zueblin/Polaron/Doc/Images/bottomview.jpg

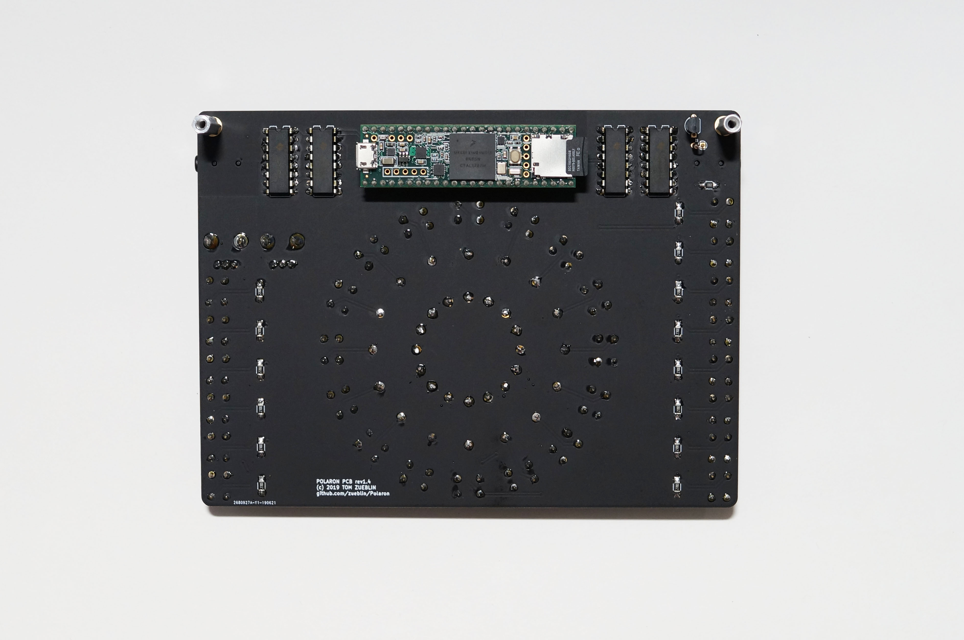
Doc/Images/bottomview.jpg
