zueblin/Polaron/Doc/Images/firmware/arduino-ide-board-selection.png

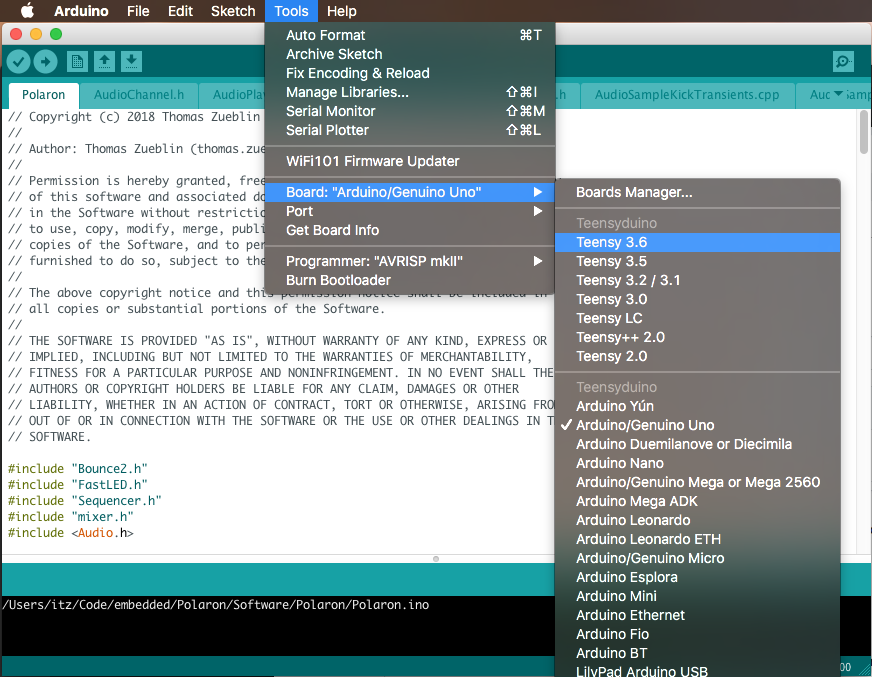
Doc/Images/firmware/arduino-ide-board-selection.png
