zueblin/Polaron/Doc/Images/firmware/arduino-ide-initial.png

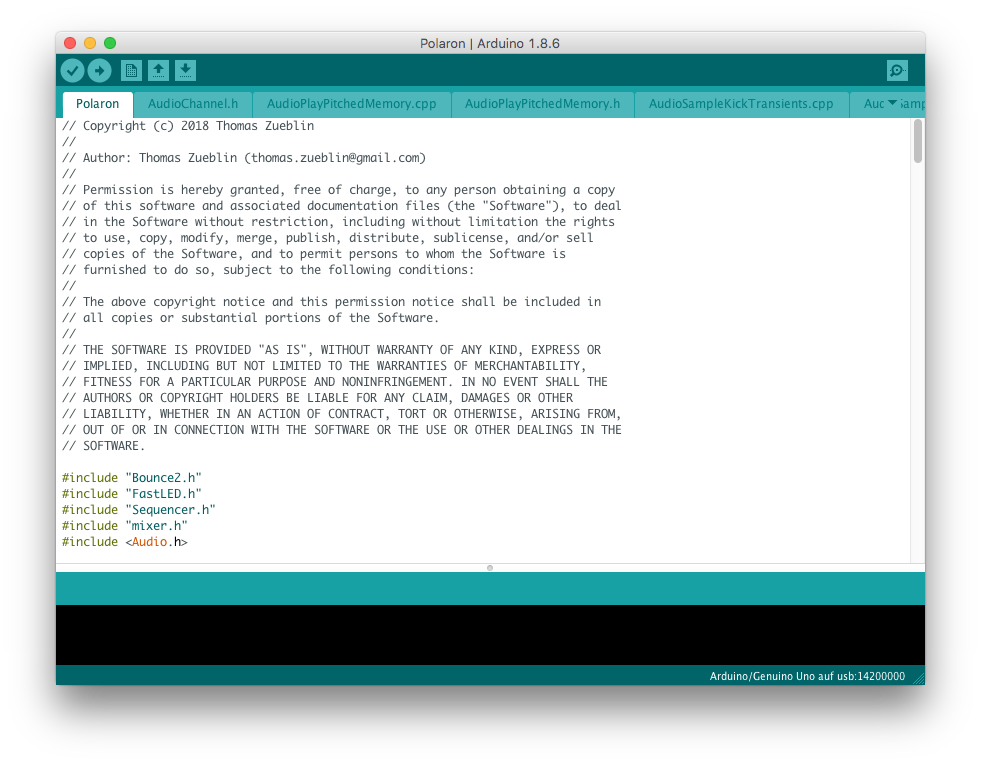
Doc/Images/firmware/arduino-ide-initial.png
