zueblin/Polaron/Doc/Images/firmware/arduino-ide-successful-compilation.png

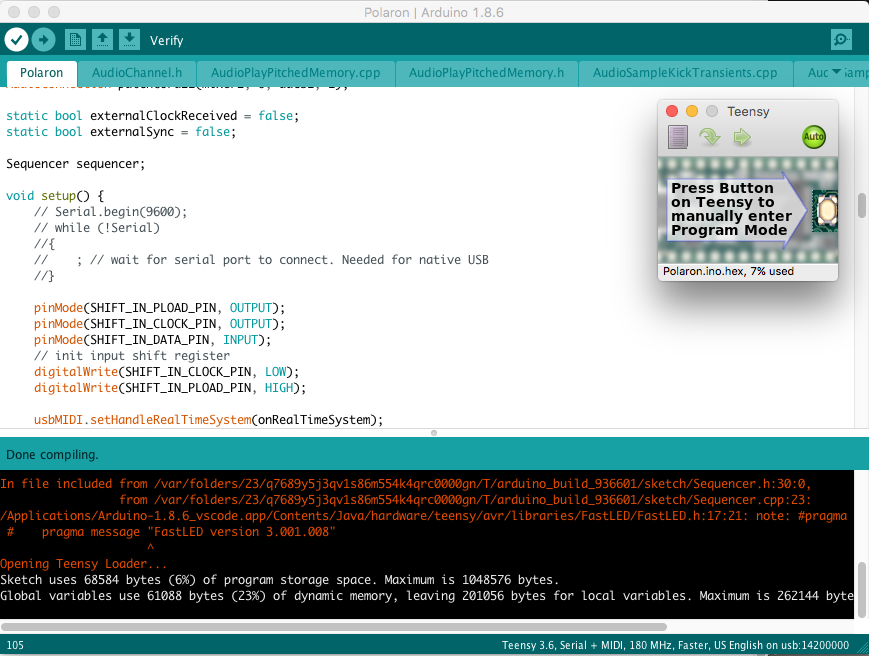
Doc/Images/firmware/arduino-ide-successful-compilation.png
