zueblin/Polaron/Doc/Images/firmware/arduino-ide-upload.png

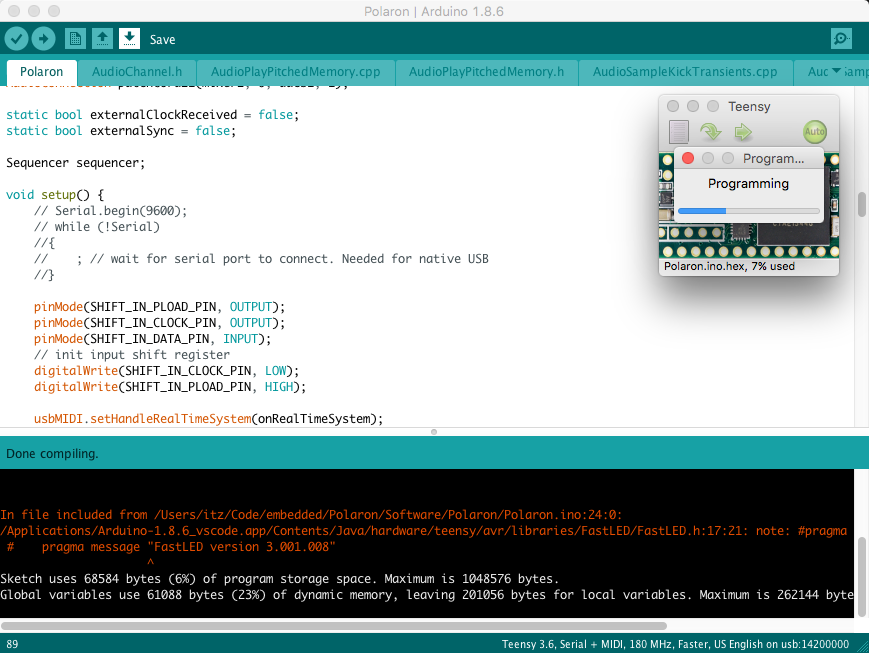
Doc/Images/firmware/arduino-ide-upload.png
