zueblin/Polaron/Doc/Images/firmware/arduino-ide-usbtype-selection.png

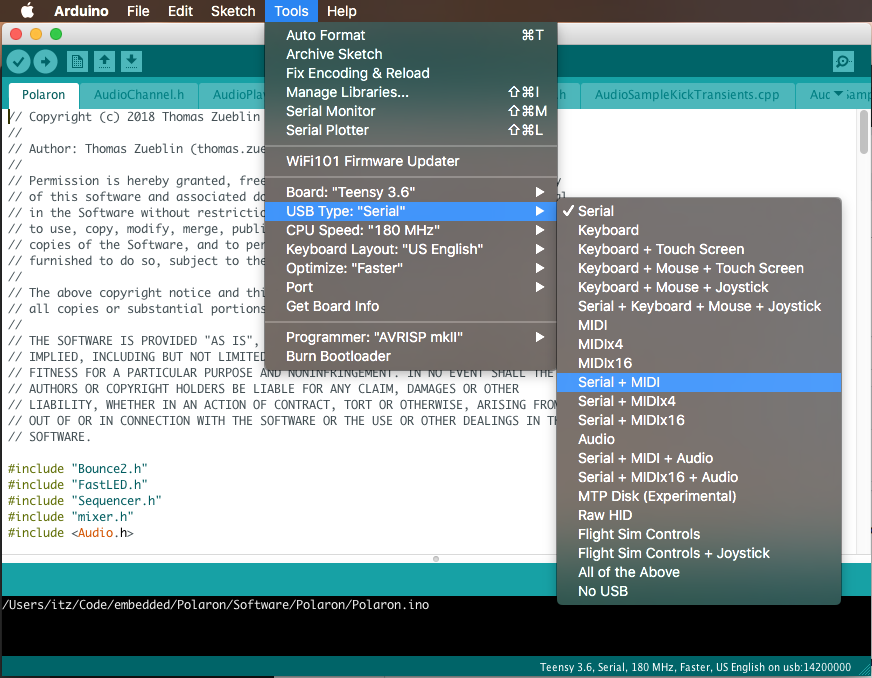
Doc/Images/firmware/arduino-ide-usbtype-selection.png
