zueblin/Polaron/Doc/Images/pcb.png

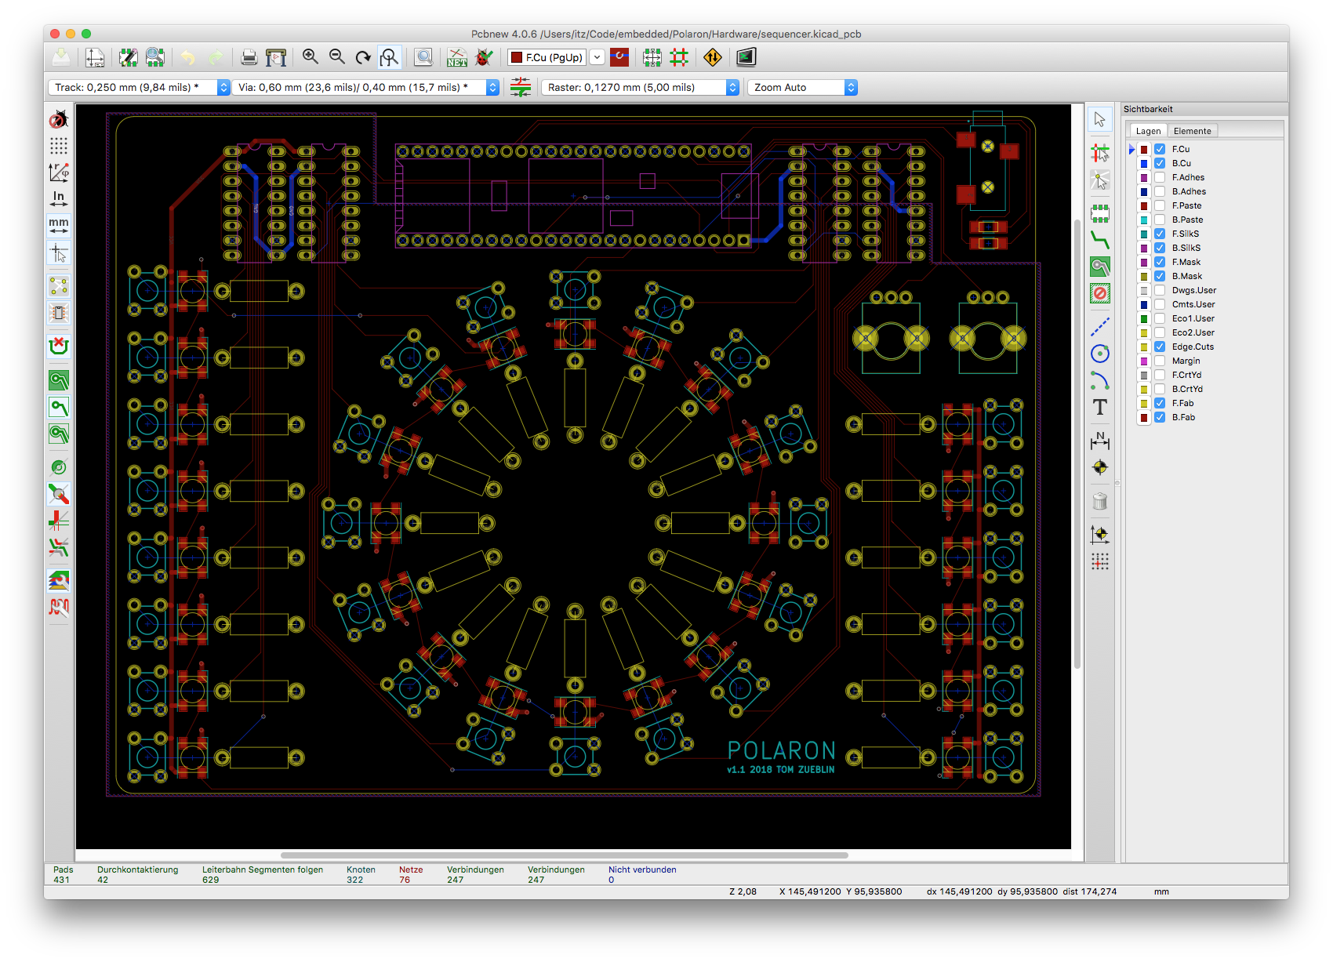
Doc/Images/pcb.png
