zueblin/Polaron/Doc/Images/topview.jpg

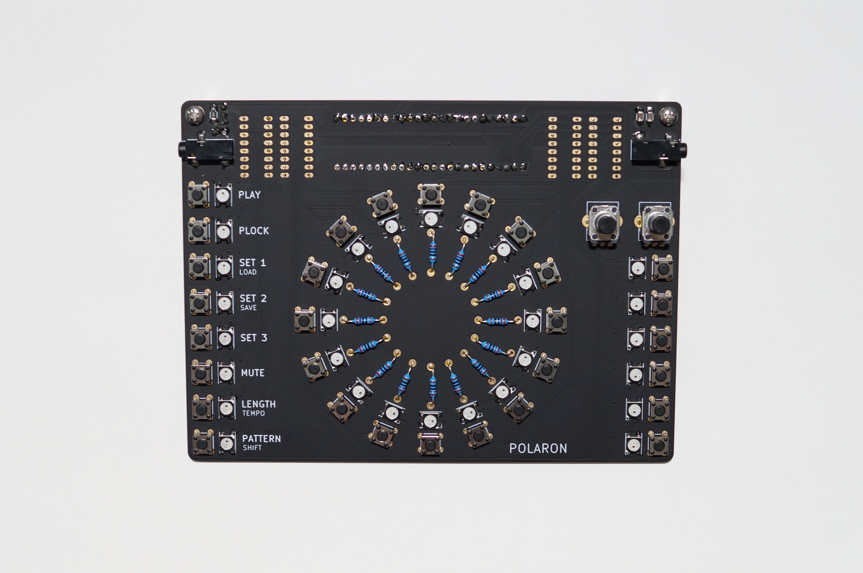
Doc/Images/topview.jpg
