zueblin/Polaron/Doc/Images/assembly/rev-1.4/parts.jpg

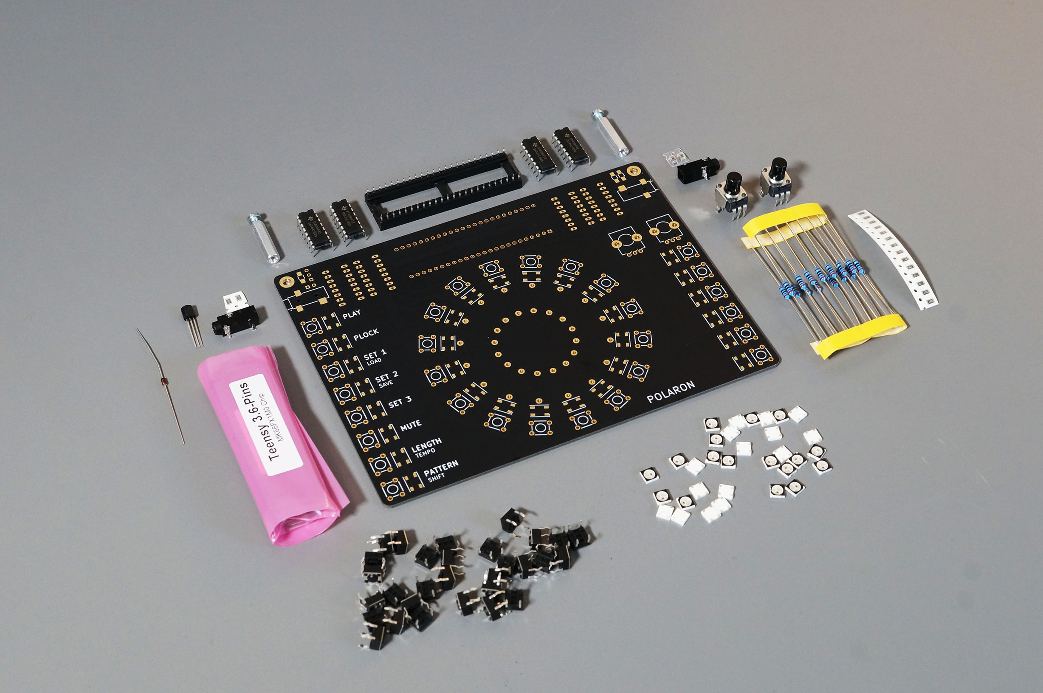
Doc/Images/assembly/rev-1.4/parts.jpg
