zueblin/Polaron/Doc/Images/assembly/done.jpg

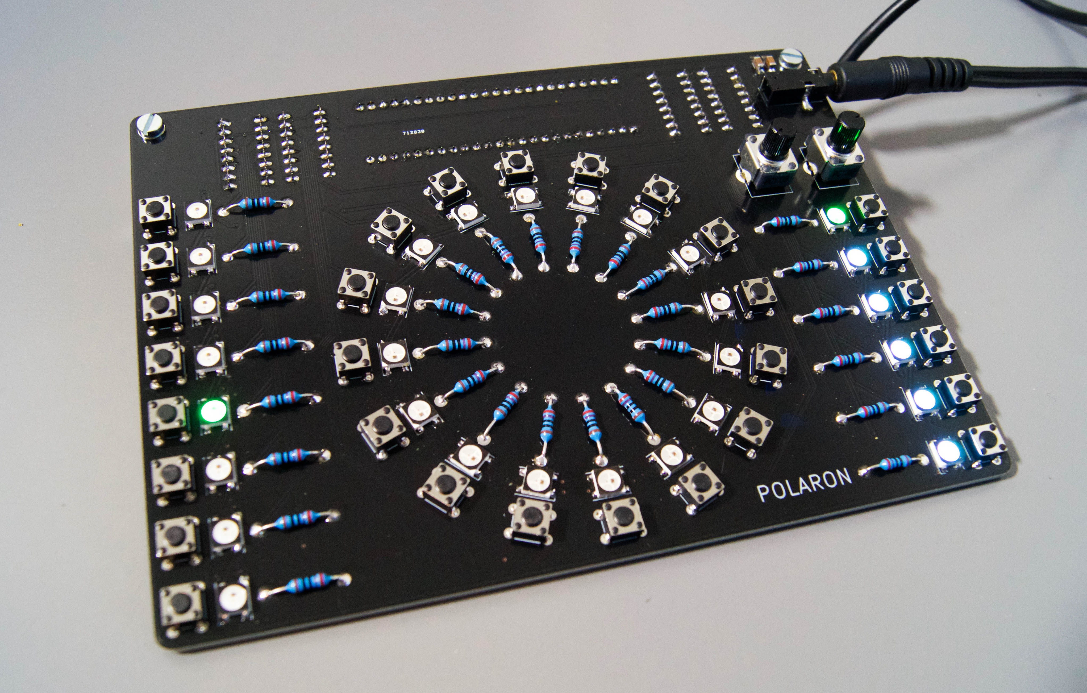
Doc/Images/assembly/done.jpg
