zueblin/Polaron/Doc/Images/assembly/led-dot-1.jpg

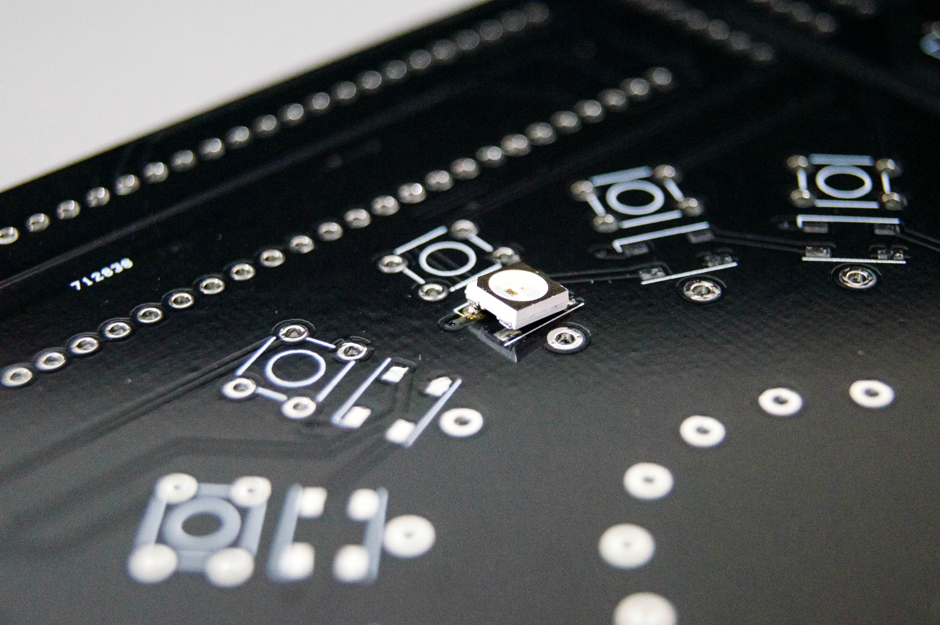
Doc/Images/assembly/led-dot-1.jpg
