zueblin/Polaron/Doc/Images/assembly/led-dot-2.jpg

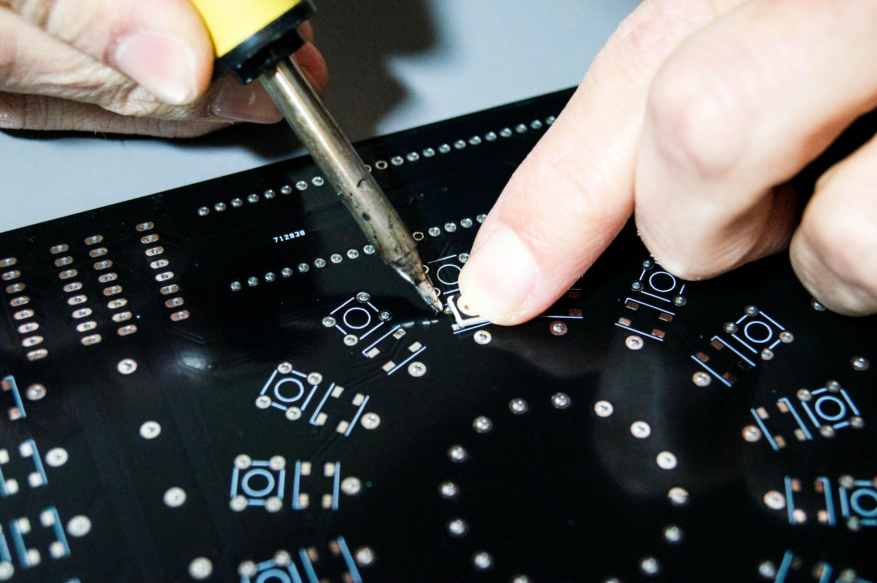
Doc/Images/assembly/led-dot-2.jpg
