zueblin/Polaron/Doc/Images/assembly/led-dot.jpg

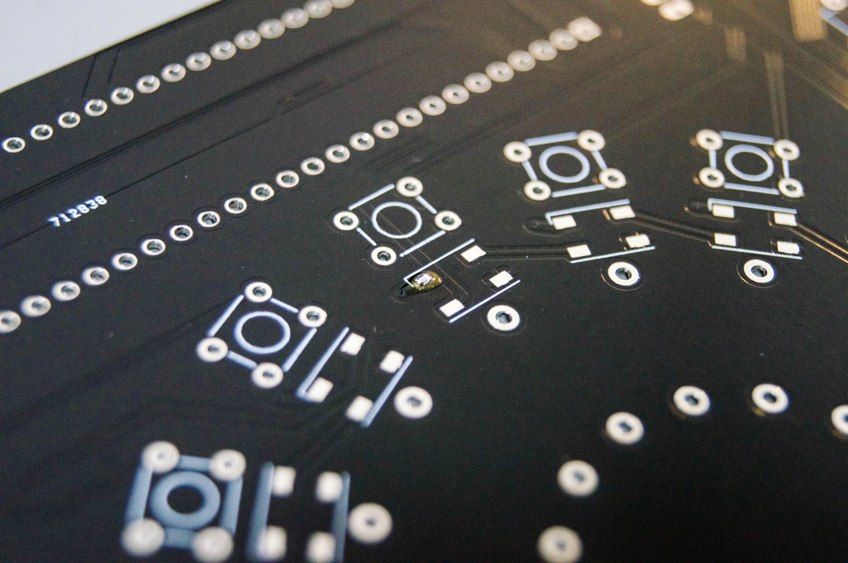
Doc/Images/assembly/led-dot.jpg
