zueblin/Polaron/Doc/Images/assembly/led-placement.jpg

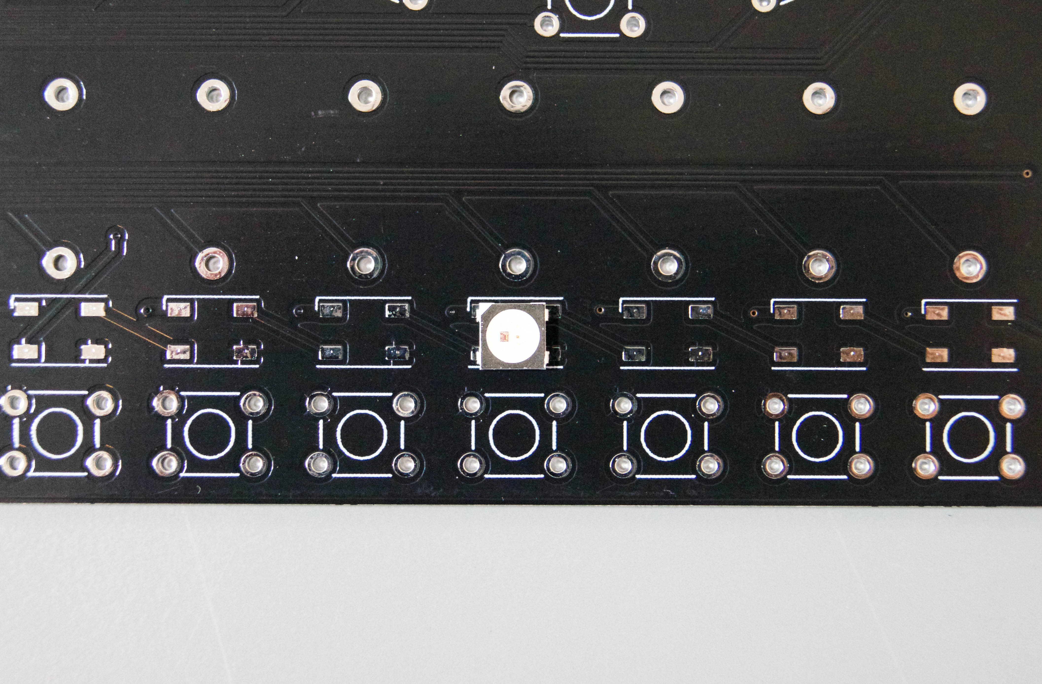
Doc/Images/assembly/led-placement.jpg
