zueblin/Polaron/Doc/Images/assembly/leds-done.jpg

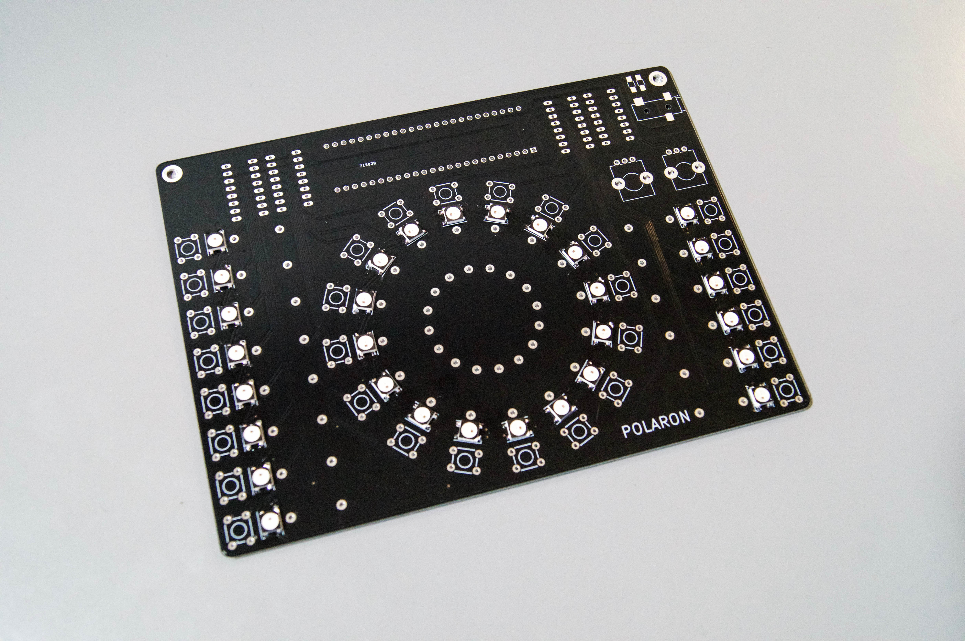
Doc/Images/assembly/leds-done.jpg
