zueblin/Polaron/Doc/Images/assembly/push-buttons.jpg

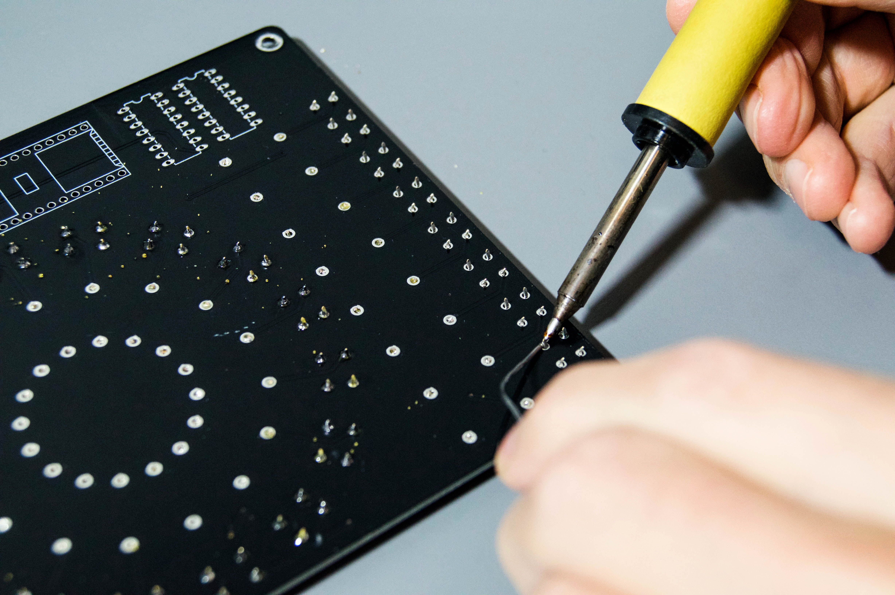
Doc/Images/assembly/push-buttons.jpg
