zueblin/Polaron/Doc/Images/assembly/resistors-1.jpg

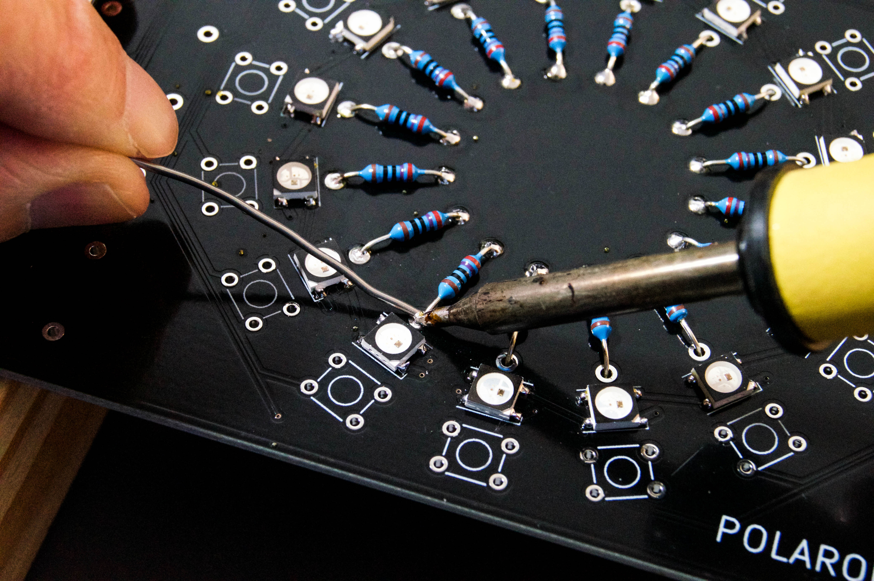
Doc/Images/assembly/resistors-1.jpg
