zueblin/Polaron/Doc/Images/assembly/resistors-cut.jpg

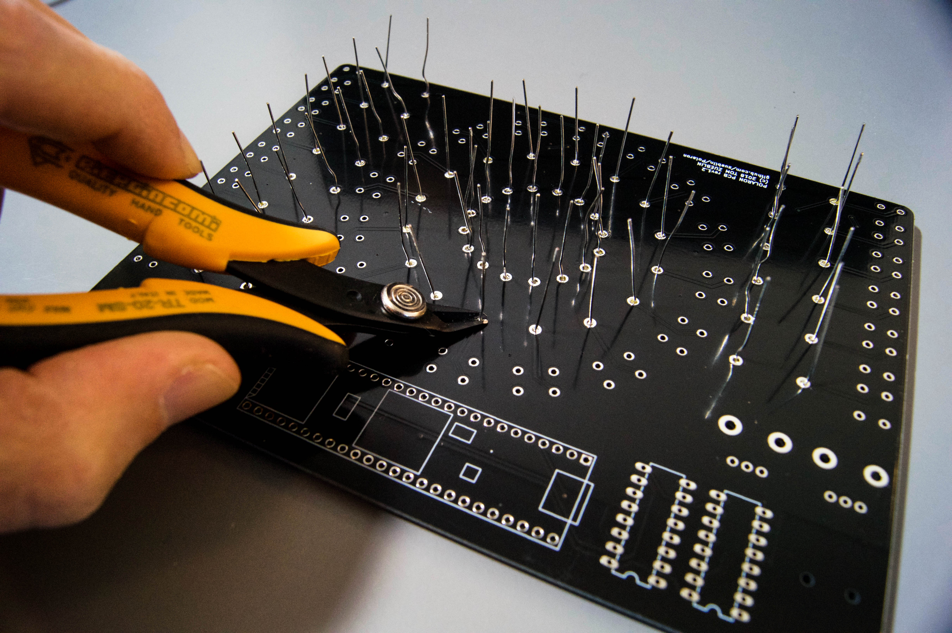
Doc/Images/assembly/resistors-cut.jpg
