zueblin/Polaron/Doc/Images/assembly/rev-1.4/audio-out-capacitors-done.jpg

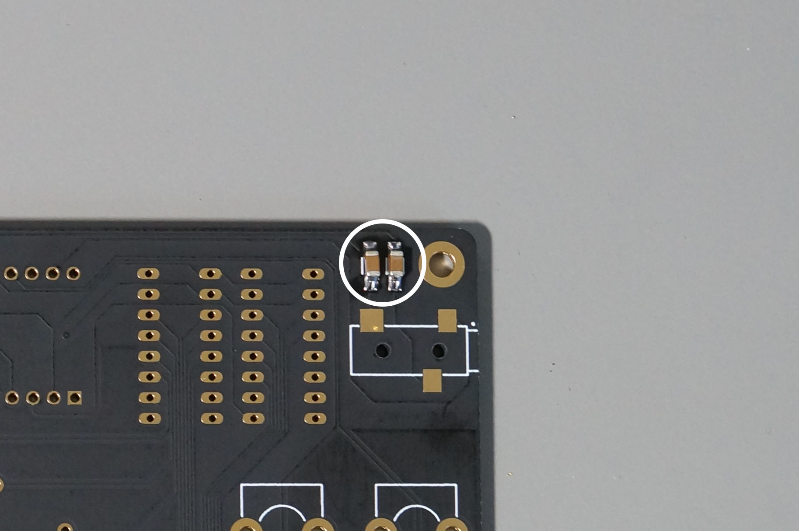
Doc/Images/assembly/rev-1.4/audio-out-capacitors-done.jpg
