zueblin/Polaron/Doc/Images/assembly/rev-1.4/led-dot-2.jpg

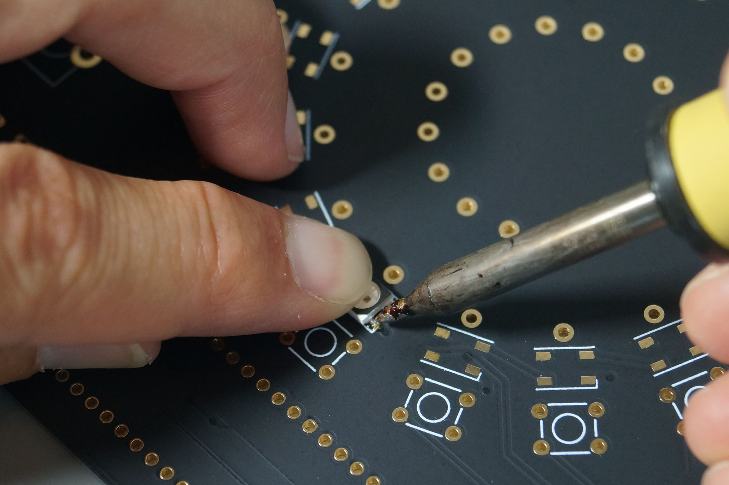
Doc/Images/assembly/rev-1.4/led-dot-2.jpg
