zueblin/Polaron/Doc/Images/assembly/rev-1.4/led-dot.jpg

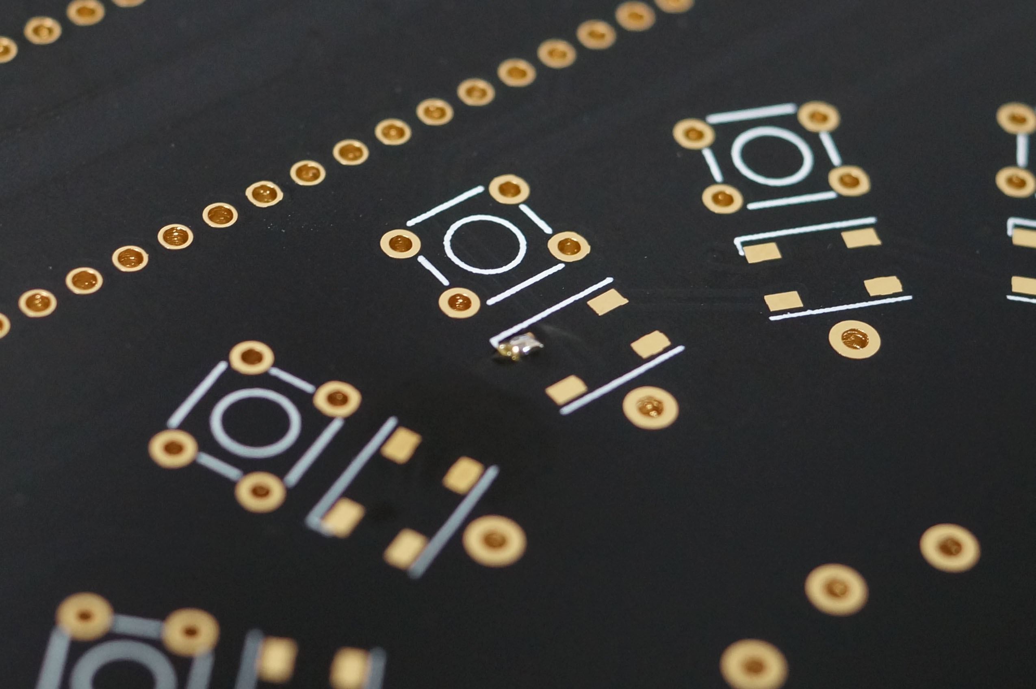
Doc/Images/assembly/rev-1.4/led-dot.jpg
