zueblin/Polaron/Doc/Images/assembly/rev-1.4/led-placement.jpg

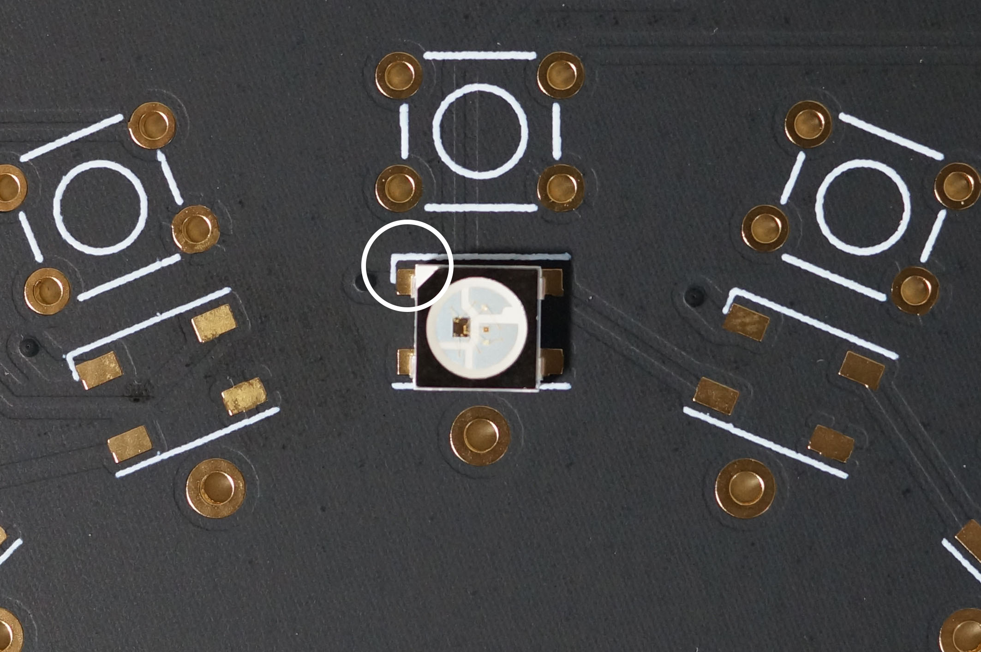
Doc/Images/assembly/rev-1.4/led-placement.jpg
