zueblin/Polaron/Doc/Images/assembly/rev-1.4/plugs-done.jpg

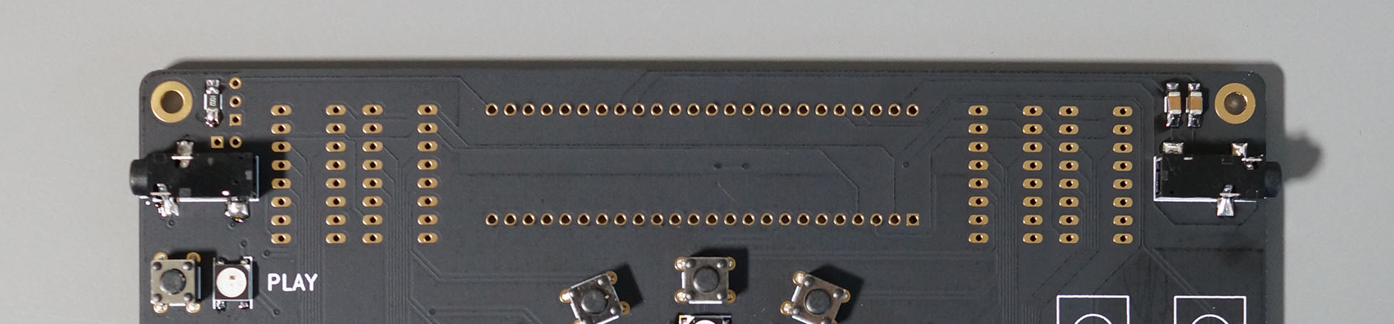
Doc/Images/assembly/rev-1.4/plugs-done.jpg
