zueblin/Polaron/Doc/Images/assembly/rev-1.4/pots-done.jpg

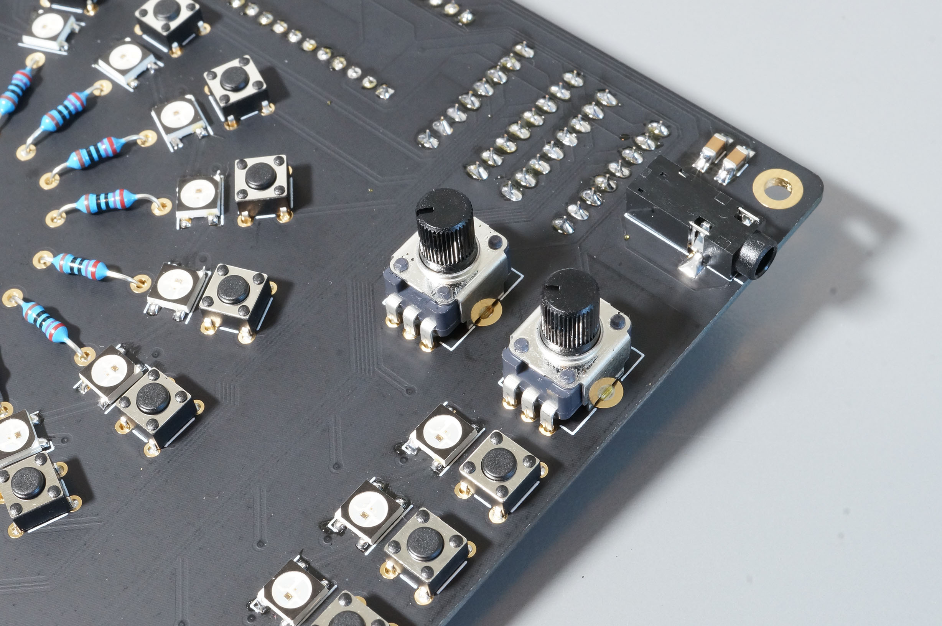
Doc/Images/assembly/rev-1.4/pots-done.jpg
