zueblin/Polaron/Doc/Images/assembly/rev-1.4/pushbuttons-done.jpg

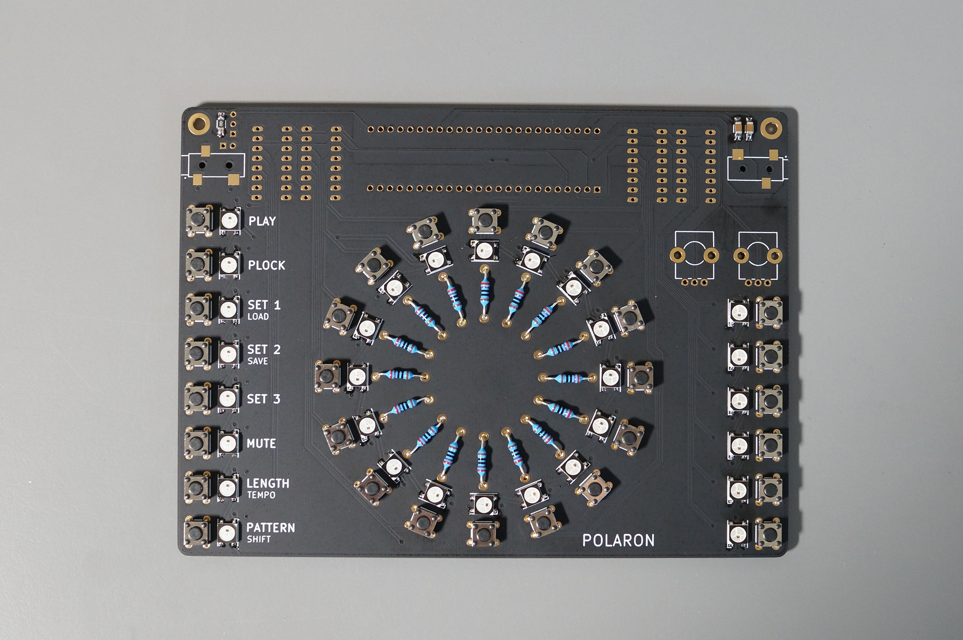
Doc/Images/assembly/rev-1.4/pushbuttons-done.jpg
