zueblin/Polaron/Doc/Images/assembly/rev-1.4/shiftregisters-done.jpg

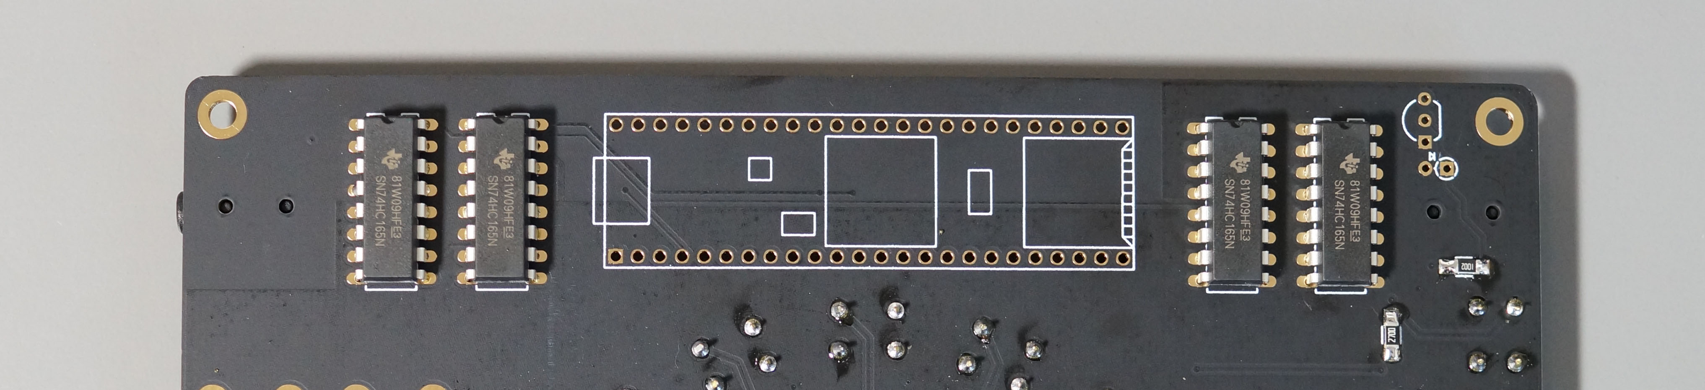
Doc/Images/assembly/rev-1.4/shiftregisters-done.jpg
