zueblin/Polaron/Doc/Images/assembly/rev-1.4/smd-resistors-done.jpg

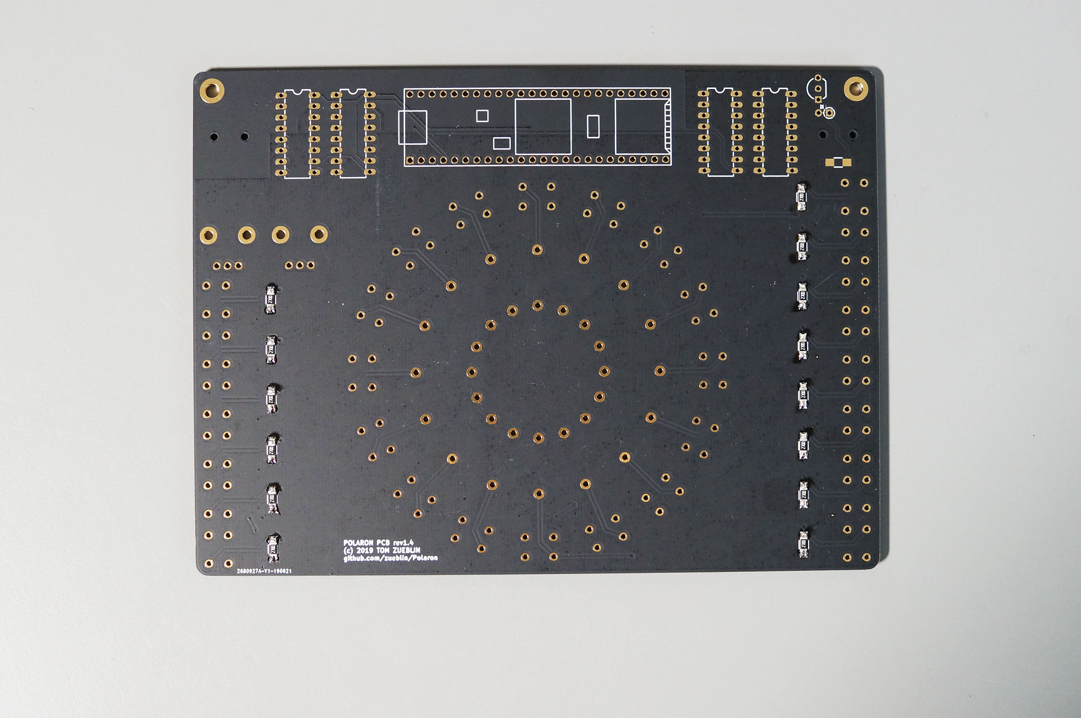
Doc/Images/assembly/rev-1.4/smd-resistors-done.jpg
