zueblin/Polaron/Doc/Images/assembly/rev-1.4/socket-pcb-done.jpg

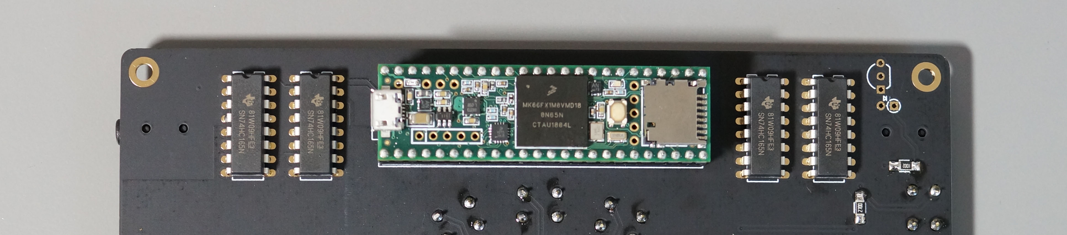
Doc/Images/assembly/rev-1.4/socket-pcb-done.jpg
