zueblin/Polaron/Doc/Images/assembly/rev-1.4/teensy-socket-done.jpg

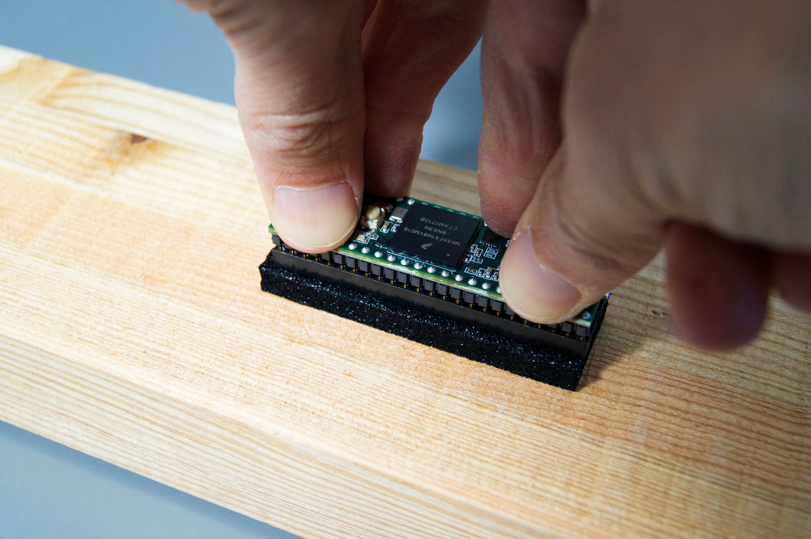
Doc/Images/assembly/rev-1.4/teensy-socket-done.jpg
