zueblin/Polaron/Doc/Images/assembly/rev-1.4/teensy-socket.jpg

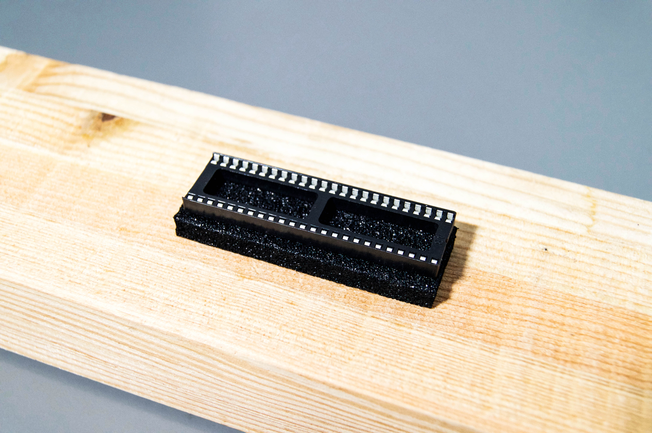
Doc/Images/assembly/rev-1.4/teensy-socket.jpg
