zueblin/Polaron/Doc/Images/assembly/rev-1.4/trigger-input-resistors-done-1.jpg

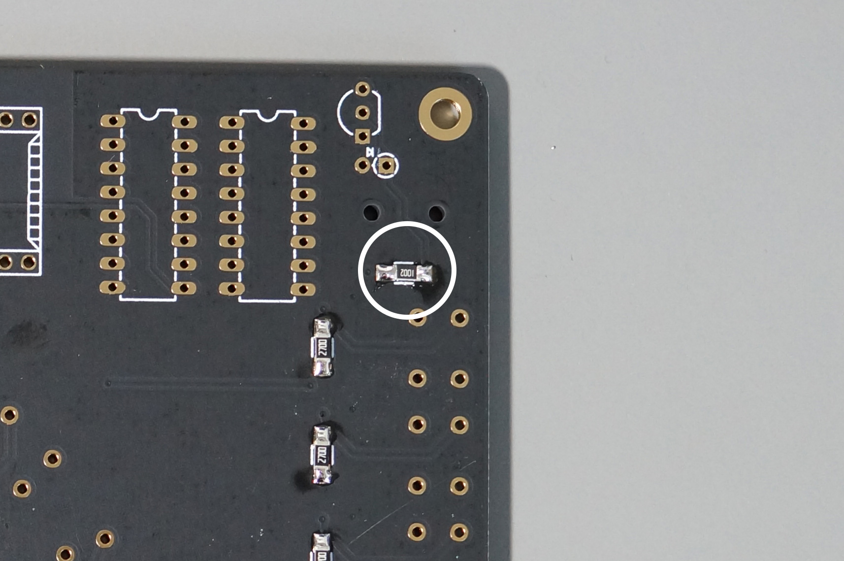
Doc/Images/assembly/rev-1.4/trigger-input-resistors-done-1.jpg
