zueblin/Polaron/Doc/Images/assembly/rev-1.4/trigger-input-transistor-and-diode-done.jpg

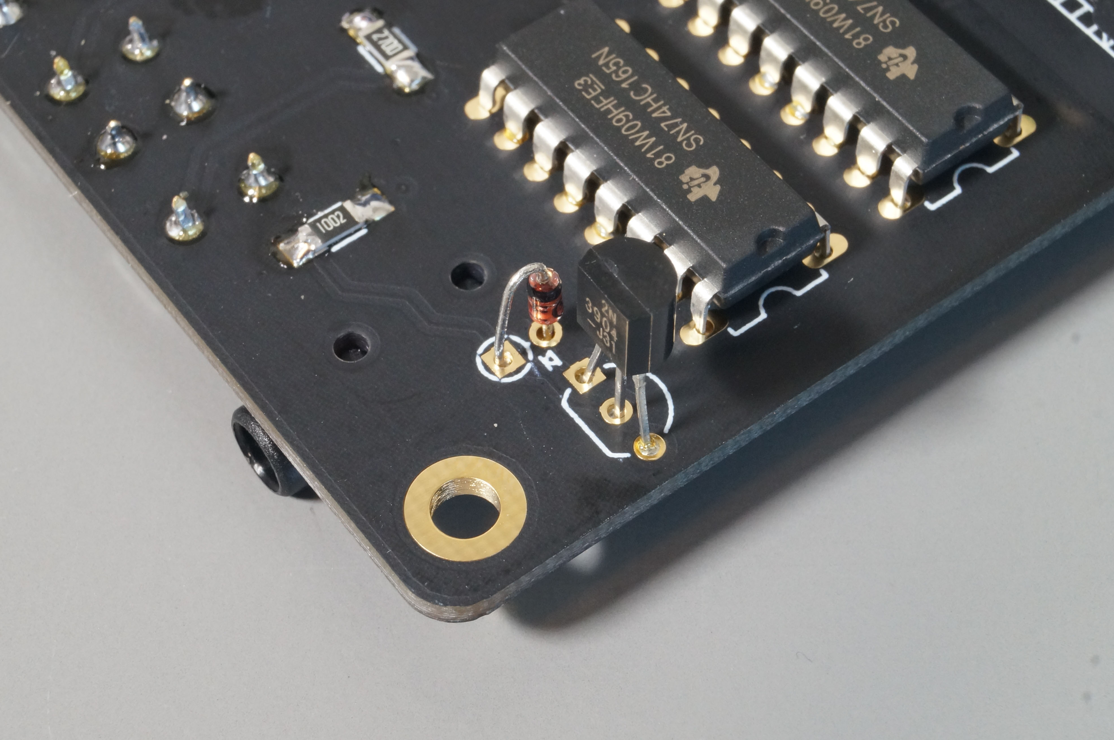
Doc/Images/assembly/rev-1.4/trigger-input-transistor-and-diode-done.jpg
