zueblin/Polaron/Doc/Images/assembly/shiftregisters-done.jpg

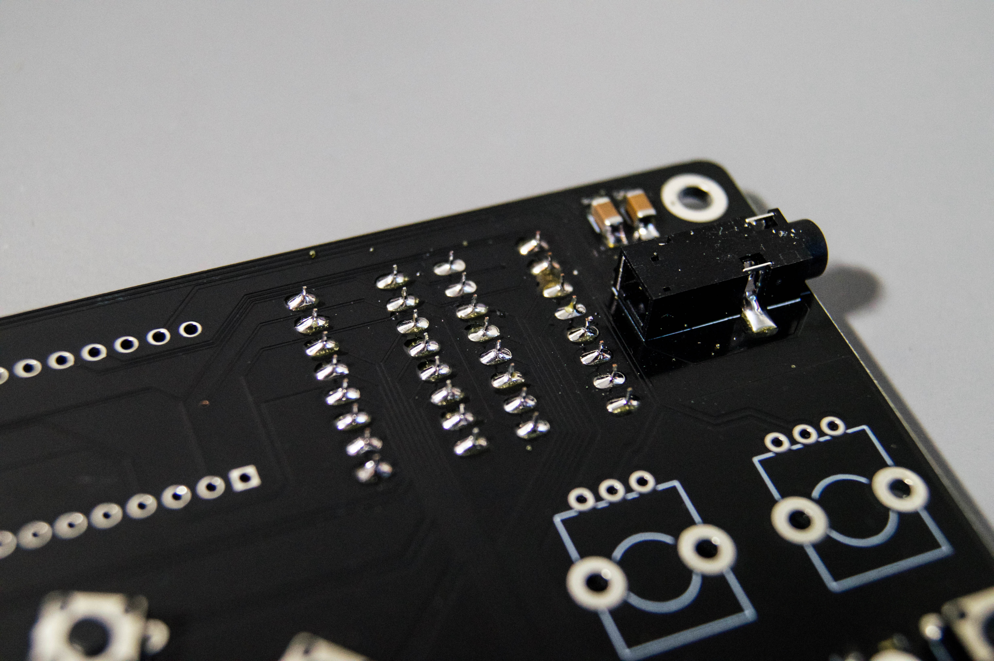
Doc/Images/assembly/shiftregisters-done.jpg
