zueblin/Polaron/Doc/Images/assembly/shiftregisters.jpg

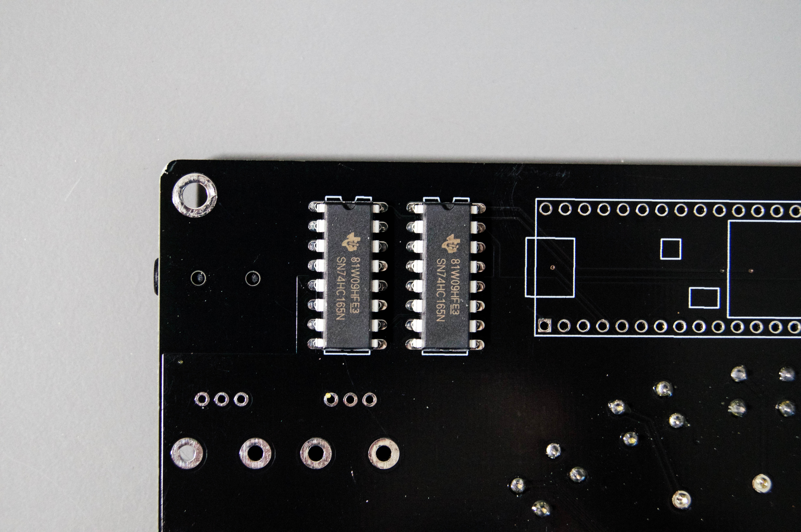
Doc/Images/assembly/shiftregisters.jpg
