zueblin/Polaron/Doc/Images/assembly/socket-pcb-done.jpg

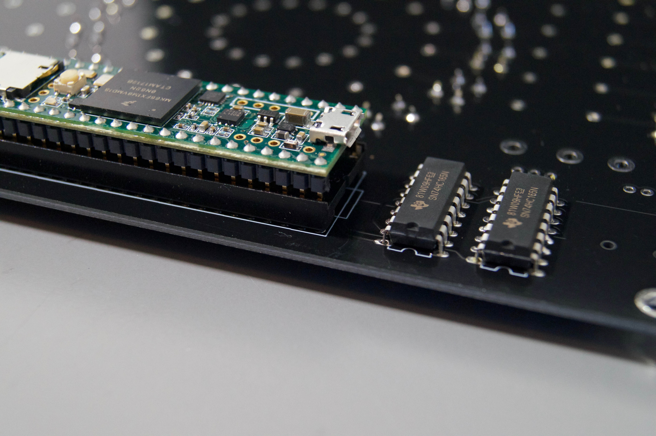
Doc/Images/assembly/socket-pcb-done.jpg
