zueblin/Polaron/Doc/Images/assembly/socket-pcb.jpg

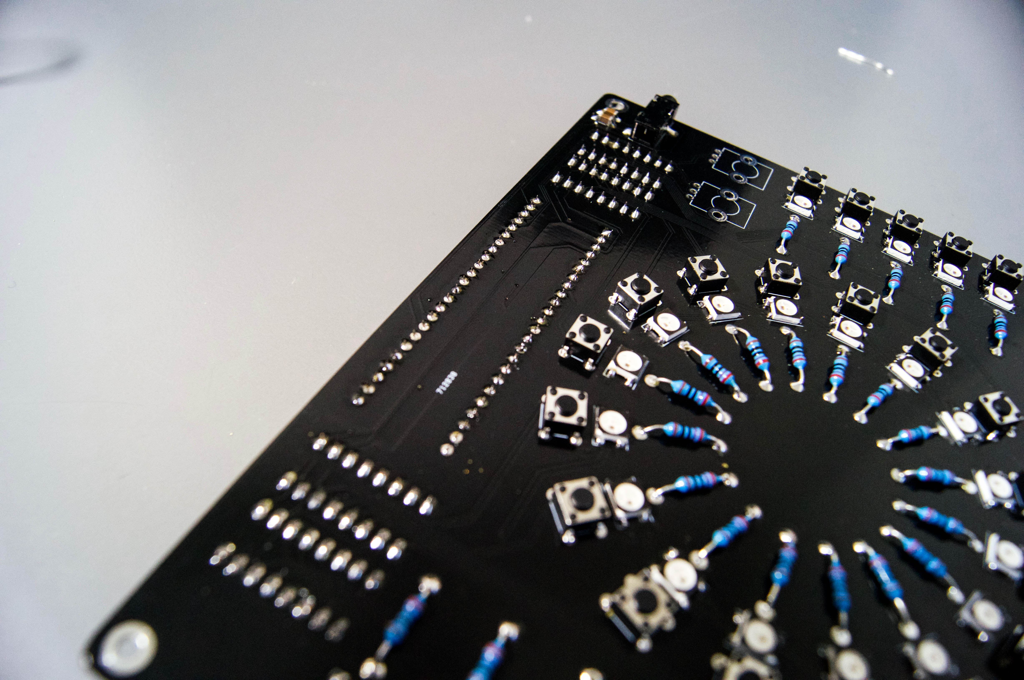
Doc/Images/assembly/socket-pcb.jpg
