zueblin/Polaron/Software/Polaron/Sequencer.h

// Copyright (c) 2018 Thomas Zueblin
//
// Author: Thomas Zueblin (thomas.zueblin@gmail.com)
//
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
#ifndef Sequencer_h
#define Sequencer_h

#include <stdint.h>

#include "AudioChannel.h"
#include "Bounce2.h"
#include "FastLED.h"
#include "Sensor.h"
#include "SequencerTrack.h"
#include "mixer.h"
#include "Clock.h"
#include "ProjectPersistence.h"

#define SHIFT_IN_DATA_PIN 1
#define TRIGGER_IN_PIN 33

#define POTI_PIN_1 A8
#define POTI_PIN_2 A9

#define NUMBER_OF_INSTRUMENTTRACKS 6
#define NUMBER_OF_FUNCTIONBUTTONS 8
#define NUMBER_OF_TRACKBUTTONS 6
#define NUMBER_OF_STEPBUTTONS 16

#define BUTTON_STARTSTOP 0
#define BUTTON_TOGGLE_PLOCK 1
#define BUTTON_SET_PARAMSET_1 2
#define BUTTON_SET_PARAMSET_2 3
#define BUTTON_SET_PARAMSET_3 4
#define BUTTON_TOGGLE_MUTE 5
#define BUTTON_SET_TRACKLENGTH 6
#define BUTTON_SET_PATTERN 7

// experimental feature: output triggers / track params as midi
// #define SEND_MIDI_OUTPUT

// led config
#define NUM_LEDS NUMBER_OF_FUNCTIONBUTTONS + NUMBER_OF_TRACKBUTTONS + NUMBER_OF_STEPBUTTONS

#define functionLED(n) leds[NUMBER_OF_STEPBUTTONS + (n)]
#define stepLED(n) leds[(n)]
#define trackLED(n) leds[NUMBER_OF_FUNCTIONBUTTONS + NUMBER_OF_STEPBUTTONS + (n)]

enum class FunctionMode {
    START_STOP,
    SET_TRACK_LENGTH,
    LEAVE_SET_TRACK_LENGTH,
    TOGGLE_PLOCKS,
    LEAVE_TOGGLE_PLOCKS,
    TOGGLE_MUTES,
    LEAVE_TOGGLE_MUTES,
    PATTERN_OPS,
    LEAVE_PATTERN_OPS,
    SET_TEMPO,
    DEFAULT_MODE,
    LOAD_PROJECT,
    SAVE_PROJECT
};
enum class PLockParamSet { SET1, SET2, SET3, SET3_2 };

class Sequencer {
   public:
    Sequencer();
    Bounce functionButtons[NUMBER_OF_FUNCTIONBUTTONS];
    Bounce trackButtons[NUMBER_OF_TRACKBUTTONS];
    Bounce stepButtons[NUMBER_OF_STEPBUTTONS];
    SequencerTrack tracks[NUMBER_OF_INSTRUMENTTRACKS];
    AudioChannel *audioChannels[NUMBER_OF_INSTRUMENTTRACKS];
    Sensor input1;
    Sensor input2;

    ProjectPersistence persistence;

    // All leds are in the same array, since i could not get the lib to work
    // with several arrays.
    CRGB leds[NUM_LEDS];

    // main method. after reading inputs, this will update the state of the sequencer
    void updateState();

    // sets two 8 channel mixer objects. these are needed in order to be able to control gain / panorama of all AudioChannels
    void setMixers(AudioMixer8 *mix1, AudioMixer8 *mix2) {
        mixerL = mix1;
        mixerR = mix2;
        for (int i = 0; i < NUMBER_OF_INSTRUMENTTRACKS; i++) {
            mixerL->gain(i, audioChannels[i]->getOutput1Gain());
            mixerR->gain(i, audioChannels[i]->getOutput2Gain());
        }
    }

    void setChannelGain(uint8_t channel, float output1Gain, float output2Gain){
        mixerL->gain(channel, output1Gain);
        mixerR->gain(channel, output2Gain);
    }

    void onMidiInput(uint8_t rtb);
    void onTriggerReceived(){clock.onTriggerReceived();};
    boolean isRunning(){return running;};
    bool anyPatternOpsArmed() { return patternOpsArmState > 0; }
    void deactivateAllPatternOpsArms() { patternOpsArmState = 0; }
    Clock clock;

   private:
    PLockParamSet pLockParamSet = PLockParamSet::SET1;

    AudioMixer8 *mixerL;
    AudioMixer8 *mixerR;

    // defines the tempochanges in percent when using the track buttons to adjust the tempochanges
    const float buttonTempoChangeMap[6] = {1.1,1.01,1.001,0.999,0.99,0.9};
    // counters used to track led button flashing 
    int8_t buttonTempoFlashMap[6] = {0,0,0,0,0,0};
    // counters used to track the note-off signal after note-on 
    int8_t triggers[6] = {0,0,0,0,0,0};
    
    uint8_t selectedTrack = 0;
    uint8_t ledFader = 0;

    uint8_t patternOpsArmState = 0;
    uint8_t triggerPattern = 0;

    // tracks state of step copy operation
    int8_t sourceStepIndex = -1;
    bool stepCopy = false;

    // tracks state of pattern copy operation
    int8_t sourcePatternIndex = -1;
    int8_t nextPatternIndex = -1;

    bool patternCopy = false;
    bool hasActivePLockReceivers = false;

    bool running = false;
    bool trackOrStepButtonPressed = false;

    FunctionMode previousFunctionMode = FunctionMode::DEFAULT_MODE;
    FunctionMode functionMode = FunctionMode::DEFAULT_MODE;
    bool shiftPressedModeChange = false;

    FunctionMode calculateFunctionMode();

    void doStep();

    void doSetTriggers();
    void doSetTrackLength();
    void doLeaveSetTrackLength();
    void doSetTrackPLock();
    void doStartStop();
    void doToggleTrackMuteArm();
    void doUpdateMutes();
    void doTurnOffPlockMode();
    void doSetTrackSelection();
    void doSetTriggerConditions();
    void doPatternOps();
    void doLeavePatternOps();
    void doSetTempo();
    void doSaveMode();
    void doLoadMode();

    void setDefaultTrackLight(uint8_t trackNum);
    void setFunctionButtonLights();

    void start();
    void stop();

    void deactivateSensors() {
        input1.deactivate();
        input2.deactivate();
    };
};

#endif /* Sequencer_h */
