zueblin/Polaron/Software/Polaron/HatsChannel.h

// Copyright (c) 2018 Thomas Zueblin
//
// Author: Thomas Zueblin (thomas.zueblin@gmail.com)
//
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
#include <Audio.h>
#include "AudioChannel.h"
#include "effect_shaped_envelope.h"
#include "mixer.h"

#ifndef HatsChannel_h
#define HatsChannel_h

class HatsChannel : public AudioChannel {
   public:
    HatsChannel()
        : w1m(w1, 0, mixer, 0),
          w2m(w2, 0, mixer, 1),
          w3m(w3, 0, mixer, 2),
          w4m(w4, 0, mixer, 3),
          w5m(w5, 0, mixer, 4),
          w6m(w6, 0, mixer, 5),
          w7m(w7, 0, mixer, 6),
          // w8m(w8, 0, mixer, 7),
          mixerFilter(mixer, 0, filter, 0),
          filterEnv(filter, 0, envelope, 0) {
        w1.amplitude(1.0f);
        w2.amplitude(1.0f);
        w3.amplitude(1.0f);
        w4.amplitude(1.0f);
        w5.amplitude(1.0f);
        w6.amplitude(1.0f);
        w7.amplitude(1.0f);

        envelope.attack(1);
        envelope.hold(0);
        envelope.decay(5);
        // envelope.sustain(0)

        mixer.gain(0, 0.7f);
        mixer.gain(1, 0.7f);
        mixer.gain(2, 0.7f);
        mixer.gain(3, 0.7f);
        mixer.gain(4, 0.7f);
        mixer.gain(5, 0.7f);
        mixer.gain(6, 0.7f);
        // mixer.gain(7, 0.0f);

        w1.begin(1.0, baseFreq, WAVEFORM_SQUARE);
        w2.begin(1.0, baseFreq * ratio1, WAVEFORM_SQUARE);
        w3.begin(1.0, baseFreq * ratio2, WAVEFORM_SQUARE);
        w4.begin(1.0, baseFreq * ratio3, WAVEFORM_SQUARE);
        w5.begin(1.0, baseFreq * ratio4, WAVEFORM_SQUARE);
        w6.begin(1.0, baseFreq * ratio5, WAVEFORM_SQUARE);
        w7.begin(1.0, baseFreq * ratio6, WAVEFORM_SQUARE);
        // w8.begin(1.0, baseFreq * ratio7, WAVEFORM_SQUARE);

        filter.setHighpass(0, 8000, 0.700);
        filter.setHighpass(1, 8000, 0.700);
        filter.setHighpass(2, 8000, 0.700);
        // filter.setLowpass(3, 15000, 0.500);
        // filter.setHighpass(3, 8000, 0.700 );
    }
    AudioStream *getOutput1() { return &envelope; }
    AudioStream *getOutput2() { return &envelope; }

    ParameterSet getDefaultParams() { return ParameterSet(300, 500, 50, 128, 10, 10); }

    void trigger() {
        w1.frequency(baseFreq);
        w2.frequency(baseFreq * ratio1 * ratioFactor1);
        w3.frequency(baseFreq * ratio2 * ratioFactor2);
        w4.frequency(baseFreq * ratio3 * ratioFactor1);
        w5.frequency(baseFreq * ratio4 * ratioFactor2);
        w6.frequency(baseFreq * ratio5 * ratioFactor1);
        w7.frequency(baseFreq * ratio6 * ratioFactor2);
        envelope.noteOn();
    }
    void setParam1(int value) {
        baseFreq = (float)map(value, 0, 1024, 10, 200);
        // w8.frequency(baseFreq * ratio7);
    }
    void setParam2(int value) {
        float mappedValue = (float)map(value, 0, 1024, 2000, 10000);
        filter.setHighpass(0, mappedValue, 0.700);
        filter.setHighpass(1, mappedValue, 0.700);
        filter.setHighpass(2, mappedValue, 0.700);
    }
    void setParam3(int value) { envelope.attack(value * 2);}
    void setParam4(int value) { envelope.decay(5 + value * 64); }
    void setParam5(int value) { ratioFactor1 = 0.5 + value / 1024.0f; }
    void setParam6(int value) { ratioFactor2 = 0.5 + value / 1024.0f; }

   private:
    float baseFreq = 40;
    float ratio1 = 2.0;
    float ratio2 = 3.0;
    float ratio3 = 4.16;
    float ratio4 = 5.43;
    float ratio5 = 6.79;
    float ratio6 = 8.21;

    // 3 params for frequency control is too much: 
    // TODO why not scan through an array with predefined, good sounding ratios? 
    // Maybe with interpolation between slots? 
    float ratioFactor1 = 1.0;
    float ratioFactor2 = 1.0;
    // float ratio7 = 10.0;
    // float ratio2 = 2.0;

    AudioSynthWaveform w1;
    AudioSynthWaveform w2;
    AudioSynthWaveform w3;
    AudioSynthWaveform w4;
    AudioSynthWaveform w5;
    AudioSynthWaveform w6;
    AudioSynthWaveform w7;
    AudioMixer8 mixer;
    AudioFilterBiquad filter;
    AudioEffectShapedEnvelope envelope;

    AudioConnection w1m;
    AudioConnection w2m;
    AudioConnection w3m;
    AudioConnection w4m;
    AudioConnection w5m;
    AudioConnection w6m;
    AudioConnection w7m;
    AudioConnection mixerFilter;
    AudioConnection filterEnv;
};
#endif
