zueblin/Polaron/Software/Polaron/AudioSampleSnare.cpp

/*
* to create these files (on mac), use sox to create a 22khz, 16bit mono raw file:
* sox source.wav --bits 16 --encoding signed-integer --rate 22050 -t raw destination.raw
* 
* use hexdump to create the data for the array below (dont forget to adjust the length of the array with number of entries)
* hexdump -v -e '16/2 "0x%04X," "\n"' 1_1.raw
*/
#include "AudioSampleSnare.h"

// 16-bit / 22050 Hz / mono raw
uint16_t AudioSampleSnare[AudioSampleSnareLength] = {
0x001F,0x0010,0x0012,0x0028,0xFFD2,0xFEFF,0xFD40,0xFC16,0xF992,0xF882,0xF4D0,0xF3AF,0xEEC1,0xEE02,0xEA84,0xEB02,
0xE6EC,0xEC64,0xEDC2,0xD9E1,0xDA54,0xE8E6,0xF03C,0xFB4B,0xFE0D,0x15BB,0x2A29,0xFA55,0xFBEB,0x2191,0x372B,0x4663,
0x4BEB,0x5381,0x625B,0x78CE,0x4773,0x2446,0x63F1,0x73DB,0x4A15,0x3CD1,0x65E4,0x636C,0x57CF,0x4F90,0x4C0F,0x3D2B,
0x3C66,0x2ACF,0x4648,0x608B,0xC076,0xDDC4,0x100E,0xEA5A,0xC9E3,0xD313,0xEE59,0xE03E,0xE3CB,0xCC27,0xC499,0xB952,
0xBAC9,0xB31D,0xB546,0xAF84,0xB43E,0xAF27,0xB727,0xB2C9,0xD14A,0xFADE,0xA18D,0x8582,0xBA61,0xFEBA,0xD482,0xCFBA,
0xFC6C,0xF0F8,0x4682,0x1B44,0xECB6,0xCD0A,0xE501,0x2F25,0x392B,0x4880,0x416A,0x451D,0x4714,0x3F98,0x4238,0x4596,
0x5791,0x6BE5,0x0E24,0x315C,0x4E1B,0x3ECE,0x732F,0x2579,0xE2F1,0x4531,0x5805,0xFE95,0x188C,0x5DE7,0x2801,0xDC0E,
0xE37F,0xEE5E,0xF3C9,0xC7EC,0xE66F,0xF059,0xE776,0xDE4E,0xCD13,0xCA49,0xBC32,0xBD3D,0xB1F4,0xBAB5,0xABBB,0xC309,
0xA320,0xD3EE,0xD02A,0x8001,0xC941,0x9C86,0xA63A,0xBF00,0xCC1D,0xE6EE,0xCFEC,0xDD3D,0xD926,0x23D4,0xD27C,0xB12B,
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
0x039A,0xF092,0x08A4,0xFB27,0xF498,0x008E,0x0527,0x0727,0x1D2A,0xF70F,0xE554,0x0041,0xFE18,0x1B55,0x0C81,0xE486,
0x0B58,0x0E10,0xEE5B,0xFB4E,0x1363,0x120E,0xEEC4,0xFDDC,0x0958,0x0DB9,0x0AA6,0x05CE,0x09F5,0x0AC2,0x26B8,0x0469,
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
};
