zueblin/Polaron/Software/Polaron/AudioSampleKickTransients.cpp

#include "AudioSampleKickTransients.h"

/*
// 16-bit / 22050 Hz / mono raw
uint16_t AudioSampleTransient1[AudioSampleTransient1Length] = {
0xFC39,0xE906,0xC93B,0xAC39,0xA6A6,0xBE9D,0xD631,0xE1FA,0xDCEC,0xDAF1,0xE1BC,0xE629,0x2B87,0x3A78,0xBAC3,0x8000,
0x80FB,0x8001,0x8028,0x8027,0x8000,0x87EF,0xA6DB,0xC022,0xDC73,0xFC92,0x1D3B,0x31F4,0x3E18,0x4757,0x5060,0x5A36,
0x64FD,0x714D,0x7CC7,0x7FFF,0x7FE0,0x7FFF,0x7FFE,0x7FF1,0x7FFF,0x7FC8,0x7FFF,0x7D45,0x7B8A,0x7F02,0x7F32,0x7FFF,
0x7FEF,0x7FFF,0x7FFF,0x7FF5,0x7FFF,0x7FEC,0x7FFF,0x7EE3,0x6C96,0x512F,0x37C3,0x2013,0x0D38,0xFC1E,0xEC8C,0xDF43,
0xD595,0xCE84,0xC540,0xBAF0,0xB0C9,0xA603,0x9AA0,0x908A,0x8746,0x8007,0x8018,0x8000,0x8007,0x8000,0x8000,0x8006,
0x8000,0x800A,0x8001,0x800D,0x8000,0x800C,0x8000,0x800A,0x8000,0x8009,0x8000,0x8007,0x8000,0x8007,0x8000,0x8005,
0x8000,0x8006,0x8000,0x8008,0x8000,0x800C,0x8000,0x8016,0x800B,0x8686,0x9158,0x9AC8,0xA34E,0xA9FE,0xB1EE,0xB993,
0xC12D,0xC93A,0xD2A3,0xDBF1,0xE517,0xEE0E,0xF82B
};

// 16-bit / 22050 Hz / mono raw
uint16_t AudioSampleTransient2[AudioSampleTransient2Length] = {
0xF8BC,0x5E9D,0x7FFF,0x7A02,0x7FFF,0x7C99,0x7FFF,0x7DB3,0x7FFF,0x7E65,0x7FFF,0x7EEC,0x7FFF,0x7F56,0x7FFF,0x7FAB,
0x7FFF,0x7FEE,0x7FF3,0x7FFF,0x7FCA,0x7FFF,0x7FAC,0x7FFF,0x7F9C,0x7FFF,0x7F8F,0x7FFF,0x7E7C,0x70E1,0x5F95,0x50F5,
0x41AD,0x3404,0x24E1,0x1662,0x0554
};
*/

// 16-bit / 22050 Hz / mono raw
uint16_t AudioSampleTransient3[AudioSampleTransient3Length] = {
0x066A,0x0A79,0x0A91,0x0C43,0x0C7B,0x0E60,0x0FD5,0x10F0,0x10C5,0x116C,0x12D7,0x12A7,0x13E4,0x14B4,0x1563,0x164E,
0x18BC,0x1BA4,0x1F3E,0x254C,0x2FE2,0x3607,0x29F6,0x2244,0x2489,0x24F6,0x2212,0x1CC0,0x1941,0x18B0,0x18C3,0x1A3B,
0x1AAC,0x1E00,0x225F,0x2A64,0x2A83,0x2EE3,0x2C54,0x0534,0xEC75,0xE767,0xE7B3,0xED4C,0xF62B,0x014A,0x07F0,0x0AA3,
0x0948,0x064E,0x0203,0xFD64,0xF74D,0xF094,0xEB1F,0xE4EF,0xDDE5,0xD629,0xD22B,0xD251,0xD34F,0xD9C8,0xE807,0xF1D9,
0xF758,0xFD95,0x01DC,0x08E4,0x146C,0x1D86,0x189A,0x1765,0x20B0,0x3221,0x434C,0x4C45,0x5498,0x5B77,0x62F9,0x6803,
0x68FE,0x62F4,0x5ABF,0x506E,0x4409,0x3606,0x253E,0x1118,0xF426,0xD39B,0xB56F,0x9B0F,0x8A7B,0x835D,0x8000,0x8353,
0x8D9E,0x9D2B,0xAEAB,0xC42B,0xD9DA,0xF098
};
