zueblin/Polaron/Software/Polaron/AudioSampleKickTransients.h

#include "Arduino.h"

#ifndef AudioSampleKickTransients_h
#define AudioSampleKickTransients_h

/*
const uint16_t AudioSampleTransient1Length = 119;
extern uint16_t AudioSampleTransient1[AudioSampleTransient1Length];

const uint16_t AudioSampleTransient2Length = 37;
extern uint16_t AudioSampleTransient2[AudioSampleTransient2Length];
*/

const uint16_t AudioSampleTransient3Length = 102;
extern uint16_t AudioSampleTransient3[AudioSampleTransient3Length];

#endif
